MontSantos/Modular-Reconfigurable-Pedalboard/fotos pedal/WhatsApp Image 2025-12-01 at 15.23.05.jpeg

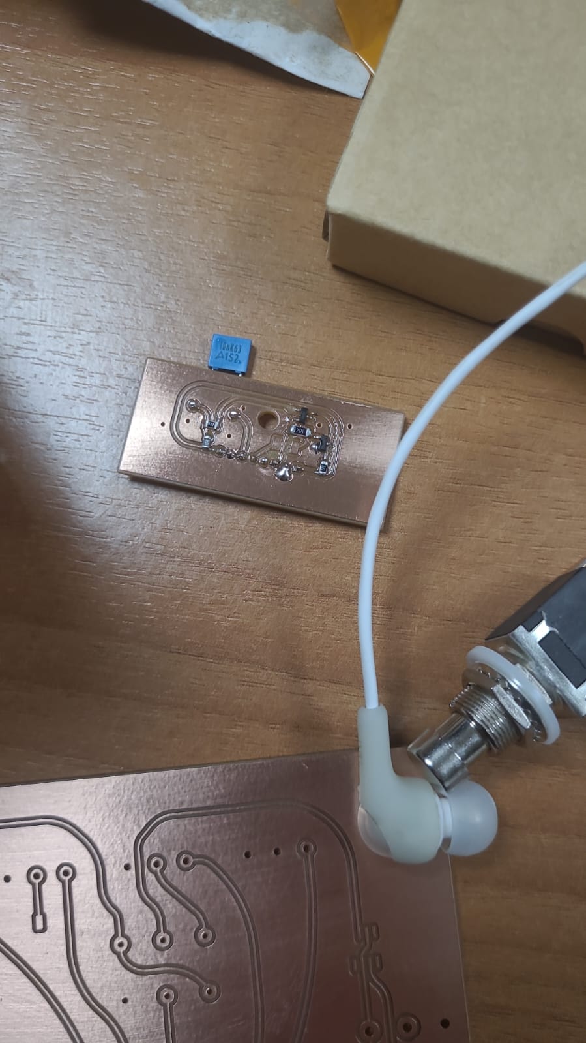
fotos pedal/WhatsApp Image 2025-12-01 at 15.23.05.jpeg
