MontSantos/Modular-Reconfigurable-Pedalboard/fotos pedal/WhatsApp Image 2025-12-11 at 19.14.50.jpeg

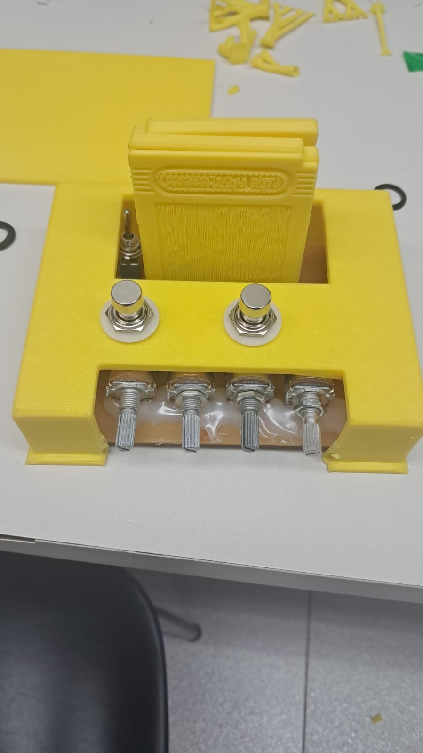
fotos pedal/WhatsApp Image 2025-12-11 at 19.14.50.jpeg
