MontSantos/Modular-Reconfigurable-Pedalboard/fotos pedal/WhatsApp Image 2025-12-11 at 19.24.07.jpeg

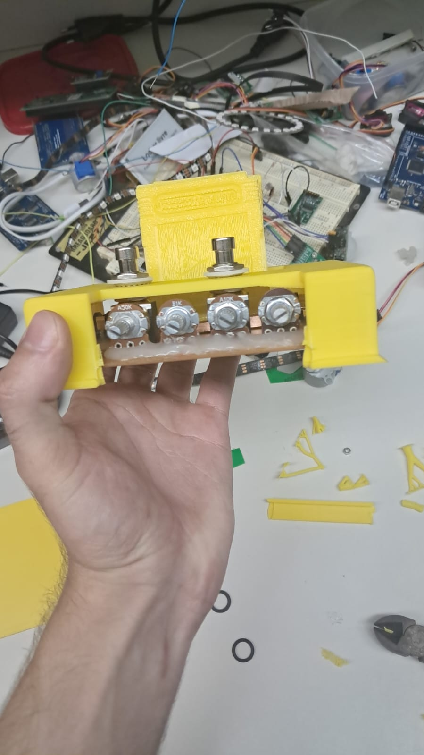
fotos pedal/WhatsApp Image 2025-12-11 at 19.24.07.jpeg
